dydx404/Information-Processing_Group_10_fpga_wand/software/cloud/backend/brain/README.md

# Legacy MVP Backend

This directory contains the earlier MVP backend implementation that predates the
current cloud app structure.

## Status

It is kept mainly for historical reference and comparison.

The canonical runtime for the current system is:

- `software/cloud/backend/versions/brain_v2_scoring`

The canonical repo-level cloud entrypoint is:

- `software/cloud/main.py`

If you are starting the current service, prefer:

- `software/cloud/start_script.sh`
