dydx404/Information-Processing_Group_10_fpga_wand/docs/README.md

# Documentation Hub

This folder is the quickest way to understand the project without reading the
entire repository tree.

## Start Here

- [newcomer_guide.md](newcomer_guide.md)
- [architecture/overview.md](architecture/overview.md)
- [testing/system_validation_report.md](testing/system_validation_report.md)
- [demo/final_runbook.md](demo/final_runbook.md)

## By Topic

- System architecture:
  [architecture/overview.md](architecture/overview.md)
- Node control over HTTP:
  [http_node_control.md](http_node_control.md)
- Testing and validation:
  [testing/test-plan.md](testing/test-plan.md)
  [testing/system_validation_report.md](testing/system_validation_report.md)
- Demo and operation:
  [demo/README.md](demo/README.md)
  [demo/final_runbook.md](demo/final_runbook.md)
- Report and team/project-management material:
  [group/](group/)
  [report/README.md](report/README.md)

## Important Note

The `group/` subtree contains archival project-management, planning,
contribution-tracking, and report-preparation material. It is useful context,
but it is not the primary entry point for the runtime architecture.

For code-oriented entrypoints, go next to:

- [../README.md](../README.md)
- [../FPGA/README.md](../FPGA/README.md)
- [../software/README.md](../software/README.md)
- [../hardware/README.md](../hardware/README.md)
