dydx404/Information-Processing_Group_10_fpga_wand/software/cloud/backend/versions/brain_v2_scoring/data/templates/clover_v1.png

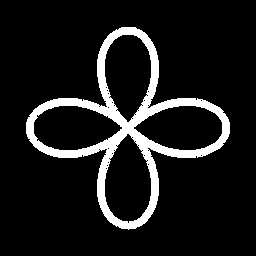
software/cloud/backend/versions/brain_v2_scoring/data/templates/clover_v1.png
